88markus88/ESP32_Anchor_Alarm/src/ePaperAnchorAlarm.h

#ifndef _ePaperAnchorAlarm_H
#define _ePaperAnchorAlarm_H

// Screen parameters
#include "screenParameters.h"

// global stuff (variables, function prototypes)
#define SECONDS (1000 * 1000)   // 1 second = 1 Mio microseconds

/************************** forward declarations *************************/

#endif // _ePaperAnchorAlarm_H
