88markus88/ESP32_Anchor_Alarm/src/global.h

// this file contains function prototypes and external definitions of variables needed by other modules

#ifndef _global_H
#define _global_H

/***************** global defines */
#define logLEVEL 2              // any output with log level <= this number is logged
#define maxLOG_STRING_LEN 240   // max len of logstring

#define maxDrawBufferLen 1600 //200  // max length of draw buffer for screen data. 
// determines graphics buffer size for historic positions, which remain only valid 
// as long as anchor position, alarm radius etc are not changed.
// with int8_t: 2 bytes , with int (int32_t) 8 bytes. ca. 400 needed for other stuff in RTC memory, so 1000 is maximum with 8 K RTC memory of ESP32
// 4K are available. 1600 is ca. 3K. Sufficient for 26,7 hours at 1 min intervals, 8,9 h for 20 sec intervals.

extern RTC_DATA_ATTR uint32_t fgndColor;
extern RTC_DATA_ATTR uint32_t bgndColor;

#define maxSleeptimeSafetyLimit 2000000000 // safety limit for deep sleep: no sleep above 2000 sec

//*************** global global variables ******************/
extern char outstring[maxLOG_STRING_LEN];
//extern HardwareSerial gpsSerial(1); // The serial connection to the GPS device

enum mainLoopMode {
  MODE_STARTED = 0,
  MODE_SELECTLINE = 1,
  MODE_CHANGEPARAM = 2,
  MODE_RUNNING = 3,
  MODE_ALARN = 4
};

enum verbosityType{
  LO  = 0,
  MED = 1,
  HI  = 2
};

enum graphWeightType{
  MINIM  = 0,
  MEDIUM = 1,
  HEAVY  = 2
};

enum powerSaveType{
  MIN = 0,
  MID = 1,
  MAX = 2
};

// defaults
#define d_anchorBearingDeg 40 
#define d_anchorDistanceM  23
#define d_alarmThreshold   10 
#define d_alarmDistanceM   40  
#define d_targetMeasurementIntervalSec 20
#define d_verbosity       HI
#define d_graphWeight     HEAVY
#define d_powerSaveMode   MIN
#define d_noGpsAlertThreshold 10

// Battery Thresholds for alert
#define BAT_VOLTAGE_THRESHOLD 3.5
#define BAT_PERCENT_THRESHOLD 10

// max. time in milliseconds to remain in menu before moving to MODE_RUNNING
#define MAX_MILLIS_IN_MENU 60*1000

struct measurementData
{
  //-- admin stuff
  int32_t startCounter;   // total counter for starts of ESP32
  bool applyInversion;   // if true, white on black. otherwise black on white

  verbosityType   verbosity;   // determines how much detail is shown in screens
  graphWeightType graphWeight; // determines how thick lines and symbols are schown in screens
  powerSaveType   PowerSaveMode; // determines degree of power saving

  
  bool buttonPressed;    // remembers if button has been pressed to acknowledge an alert
  bool alertON;          // remembers if an alert has been triggered
  bool validGPSLocation; // true if valid gps location, otherwise false
  mainLoopMode currentMode; // current main loop mode
  bool preferencesChanged;     // flag to indicate that a preference has been changed
  bool powerSaveChanged;       // flag to indicate that power save mode has changed
  bool graphBufferClearingNeeded; // flag to indicate that graphics buffer must be cleared
  bool newAnchorPosNeeded;     // flag to indicate that anchor position needs to be updated
 
  int32_t targetMeasurementIntervalSec; // sleep time target in seconds, controls the measurement
  char actConfigString[200];  // shows info about current configuration
  uint16_t linesInConfigString; // number of lines contained in config string

  // anchor and alarm stuff
  float anchorBearingDeg;      // anchor angle in degrees
  float anchorDistanceM;       // anchor distance in meters
  int32_t alarmThreshold;      // number of position deviations before alarm is triggered
  float alarmDistanceM;        // alarm distance in meters

  double anchorLat;            // anchor latitude
  double anchorLon;            // anchor longitude

  int32_t drawCount;           // counter for display updates
  uint8_t drawBuffer[maxDrawBufferLen][2];         // buffer for display data
  double stdDevX;             // Standard deviation of measurements in X [m]
  double stdDevY;             // Standard deviation of measurements in Y [m]
  
  double actLat;               // actual latitude
  double actLon;               // actual longitude
  float actAnchorBearingDeg;   // anchor angle in degrees
  float actAnchorDistanceM;    // anchor distance in meters
  double actHDOP;              // GPS HDOP
  int32_t SatCnt;              // GPS visible satellites
  double alertCount;           // counter for alert condition. Counts up, alert when wData.alarmThreshold exceeded
  uint32_t noAlertsSounded;    // counter for how often an alert has sounded
  char alertReasonString[80];  // reason for alert
  int32_t alertReason;         // bitmask rason for alert 
  int32_t noGpsCount;          // counter for "no gps signal" detected
  int32_t noGpsAlertThreshold; // threshold for number of "no gps signal detected" which causes alert

  float batteryVoltage;        // Voltage of battery
  float batteryPercent;        // Percentage of charge remaining in battery, calculated
};
extern RTC_DATA_ATTR measurementData wData;

//*************** function prototypes ******************/
void testDisplay();
void testDisplayWeAct();
void initDisplay(int startCounter, int fullInterval); // start display
void endDisplay(int mode);                  // power off display if mode =0 else hibernate
void logOut(int logLevel, char* str);
void buzzer(uint16_t number, uint16_t duration, uint16_t interval);
//void getInputMainScreen();
void drawInputMainScreen();
void drawInputHeader();
void drawInputData();
void drawTriangle(bool visible, int16_t xpos, int16_t ypos);
void drawWatchScreen();
void setScreenParameters();
void doParallelBuzzer(uint16_t number, uint16_t duration, uint16_t interval);
void showWelcomeMessage(boolean clearScreen, char* nextMessage, uint16_t msgLines);
void calcGraphStdDevXY();
boolean gpsReEstablished(int32_t secs);
void smartDelay(unsigned long ms);
void handleExt0Wakeup();
uint32_t print_wakeup_reason(); 

boolean gpsTest();

#endif // _global_H
